Gabrielgr01/Proyecto2_ALU/Verilog/sources/Not.v

`timescale 1ns / 1ps
//////////////////////////////////////////////////////////////////////////////////
// Company: 
// Engineer: 
// 
// Create Date: 10/07/2021 11:39:35 PM
// Design Name: 
// Module Name: Not
// Project Name: 
// Target Devices: 
// Tool Versions: 
// Description: 
// 
// Dependencies: 
// 
// Revision:
// Revision 0.01 - File Created
// Additional Comments:
// 
//////////////////////////////////////////////////////////////////////////////////


module Not(
    input IN,
    output OUT
    );
    assign OUT=~IN;
endmodule
